Discovery-Tr/AKILLI-KAPI-KILIDI-RF-WEB-CONTROL-SMART-DOOR-LOCK/Foto/20210627_210150.jpg

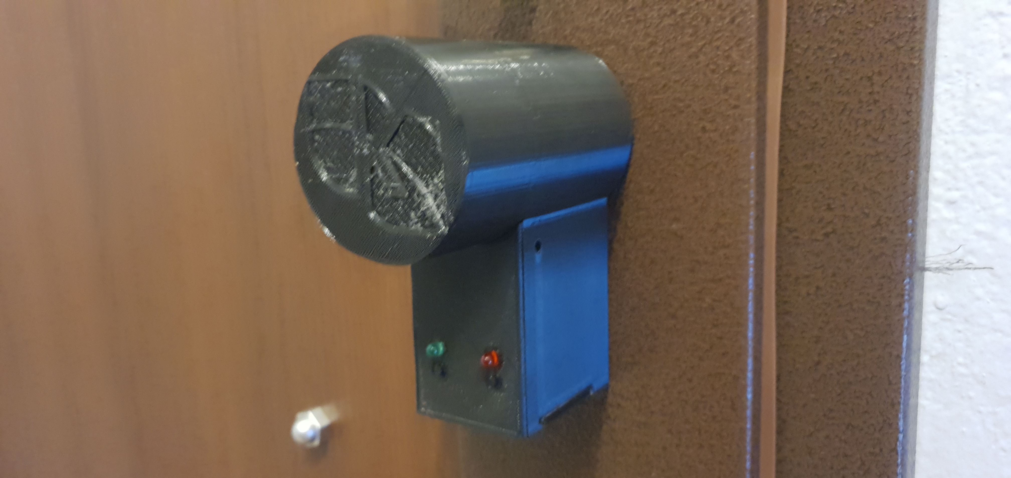
Foto/20210627_210150.jpg
