Discovery-Tr/AKILLI-KAPI-KILIDI-RF-WEB-CONTROL-SMART-DOOR-LOCK/Foto/3D Aşamalar1.JPG

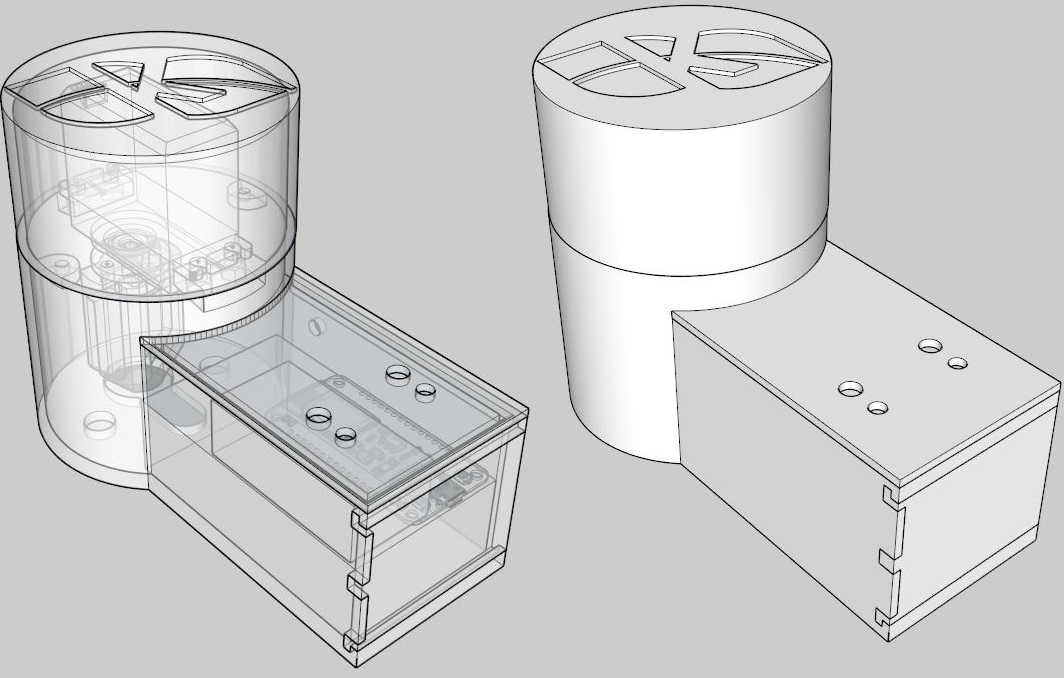
Foto/3D Aşamalar1.JPG
