Discovery-Tr/AKILLI-KAPI-KILIDI-RF-WEB-CONTROL-SMART-DOOR-LOCK/Foto/433-mhz-rf-kablosuz-alicireciver-13180-85-O.jpg

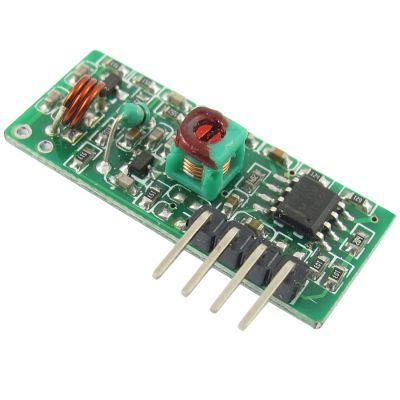
Foto/433-mhz-rf-kablosuz-alicireciver-13180-85-O.jpg
