Discovery-Tr/AKILLI-KAPI-KILIDI-RF-WEB-CONTROL-SMART-DOOR-LOCK/Foto/Discovery-Door-locks (3).JPG

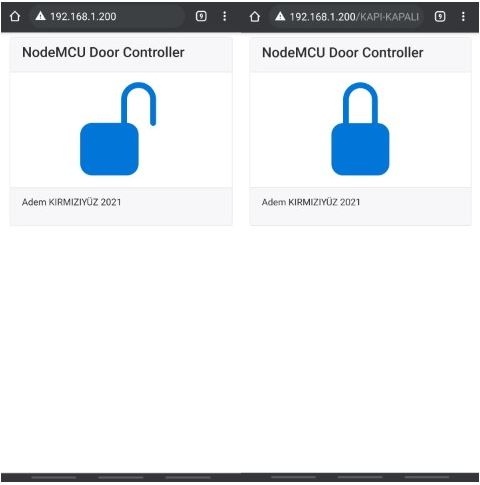
Foto/Discovery-Door-locks (3).JPG
