Discovery-Tr/AKILLI-KAPI-KILIDI-RF-WEB-CONTROL-SMART-DOOR-LOCK/Foto/Discovery-Door-locks (4) (Küçük).jpg

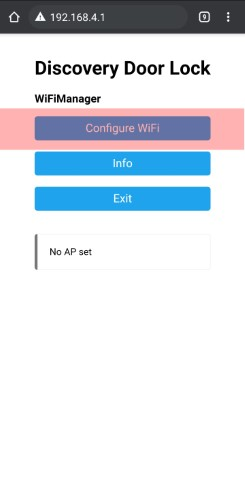
Foto/Discovery-Door-locks (4) (Küçük).jpg
