Discovery-Tr/AKILLI-KAPI-KILIDI-RF-WEB-CONTROL-SMART-DOOR-LOCK/Foto/mg996r-yuksek-torklu-servo-motor-180-derece-metal.jpeg

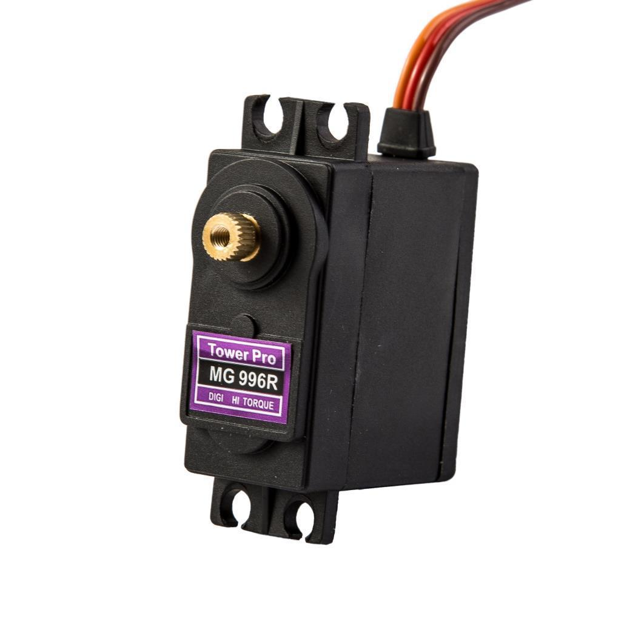
Foto/mg996r-yuksek-torklu-servo-motor-180-derece-metal.jpeg
